M17-Project/Module_17/hardware/wiring/alinco/alinco.png

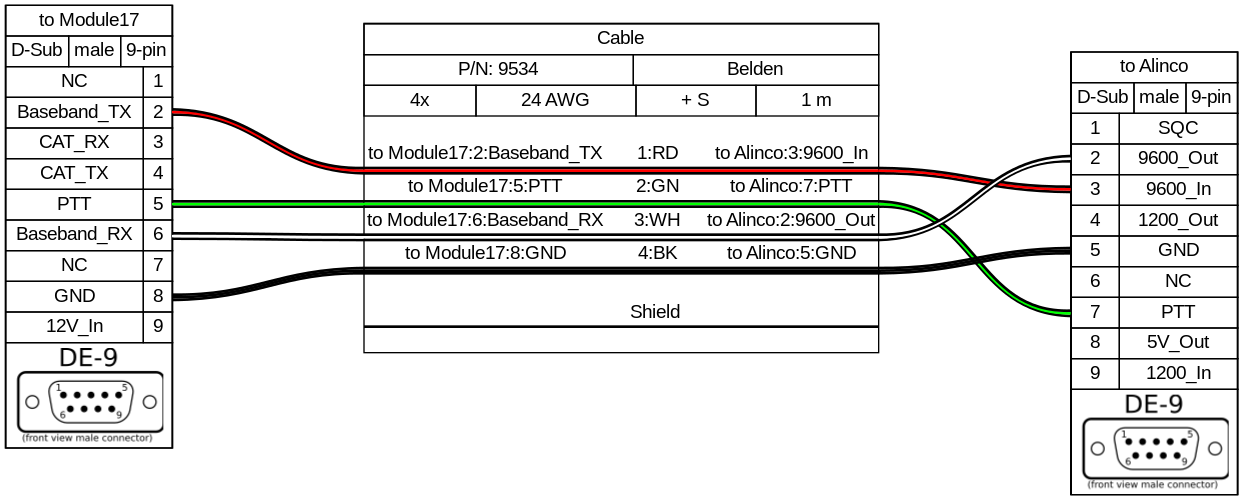
hardware/wiring/alinco/alinco.png
