M17-Project/Module_17/docs/wiring/generic/6pin_miniDIN.yml

connectors:
  DE-9:
    type: D-Sub
    image: 
      src: dsub9.svg
    subtype: male
    pinlabels: [NC, Baseband_TX, CAT_RX, CAT_TX, PTT, Baseband_RX, NC, GND, 12V_In]
  miniDIN-6:
    type: 6-pin miniDIN
    image:
      src: minidin6.png
    subtype: male
    pinlabels: [Data_In, GND, PTT, RX 9600, RX 1200, PK SQL]

cables:
  Belden 9536:
    gauge: 24 AWG
    length: 1
    colors: [BK, WH, RD, GN, BN, BU]
    wirecount: 6
    shield: false
    notes: "Belden 9536 cable has no shield"
    pn: "9536"
    manufacturer: "Belden"

connections:
  -
    - DE-9: [2,5,6,8]
    - Belden 9536: [1,2,3,4]
    - miniDIN-6: [1,3,4,2]
